MWelding/VHFPanel/images/IMG_4560.jpeg

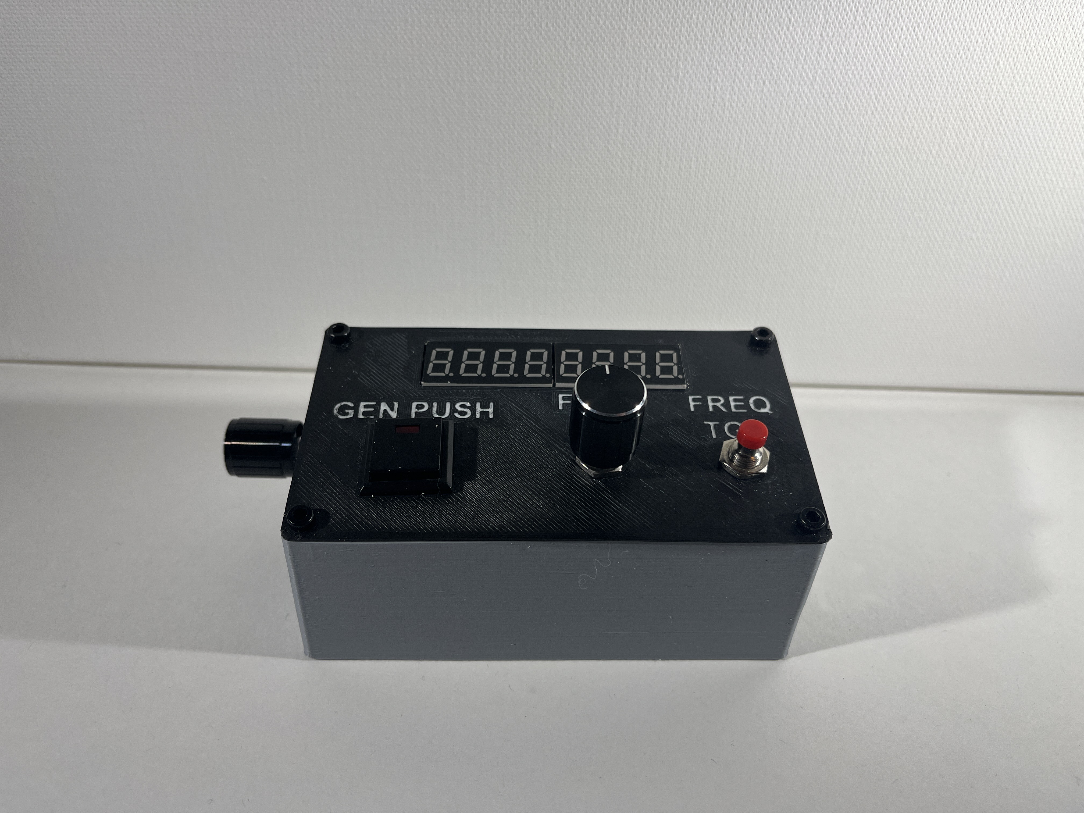
images/IMG_4560.jpeg
