MWelding/VHFPanel/images/IMG_4561.jpeg

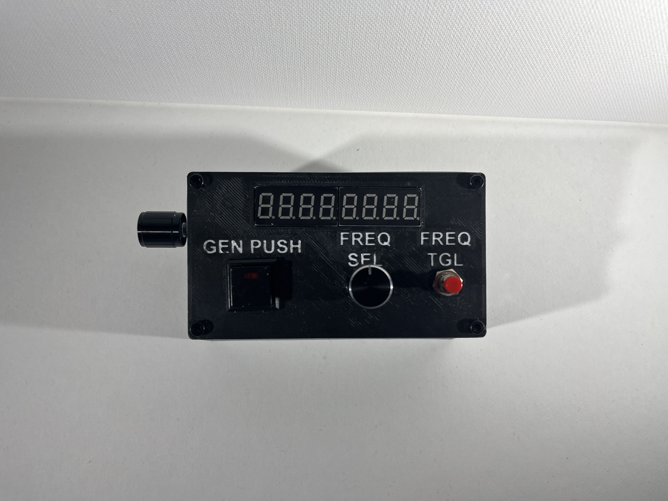
images/IMG_4561.jpeg
