MWelding/VHFPanel/images/IMG_4578.jpeg

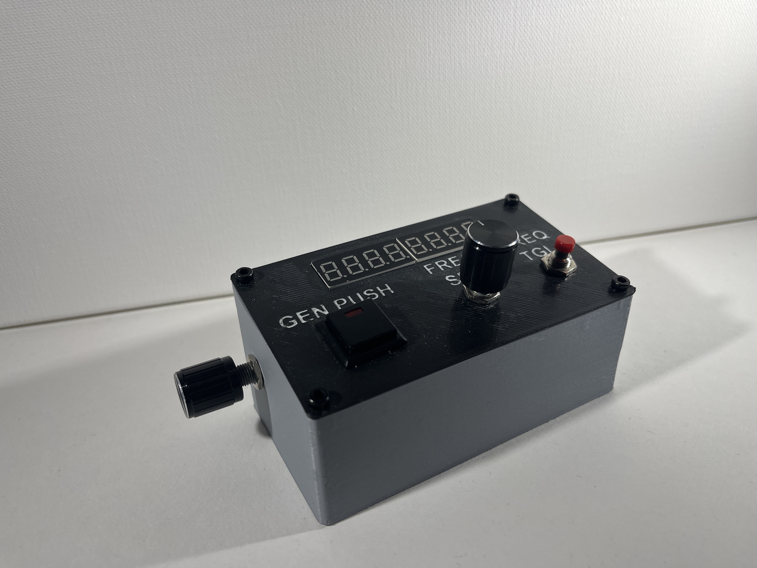
images/IMG_4578.jpeg
